sethvoltz/launch_control/media/build-photos/05 - Component detail sketch - USB female socket.jpg

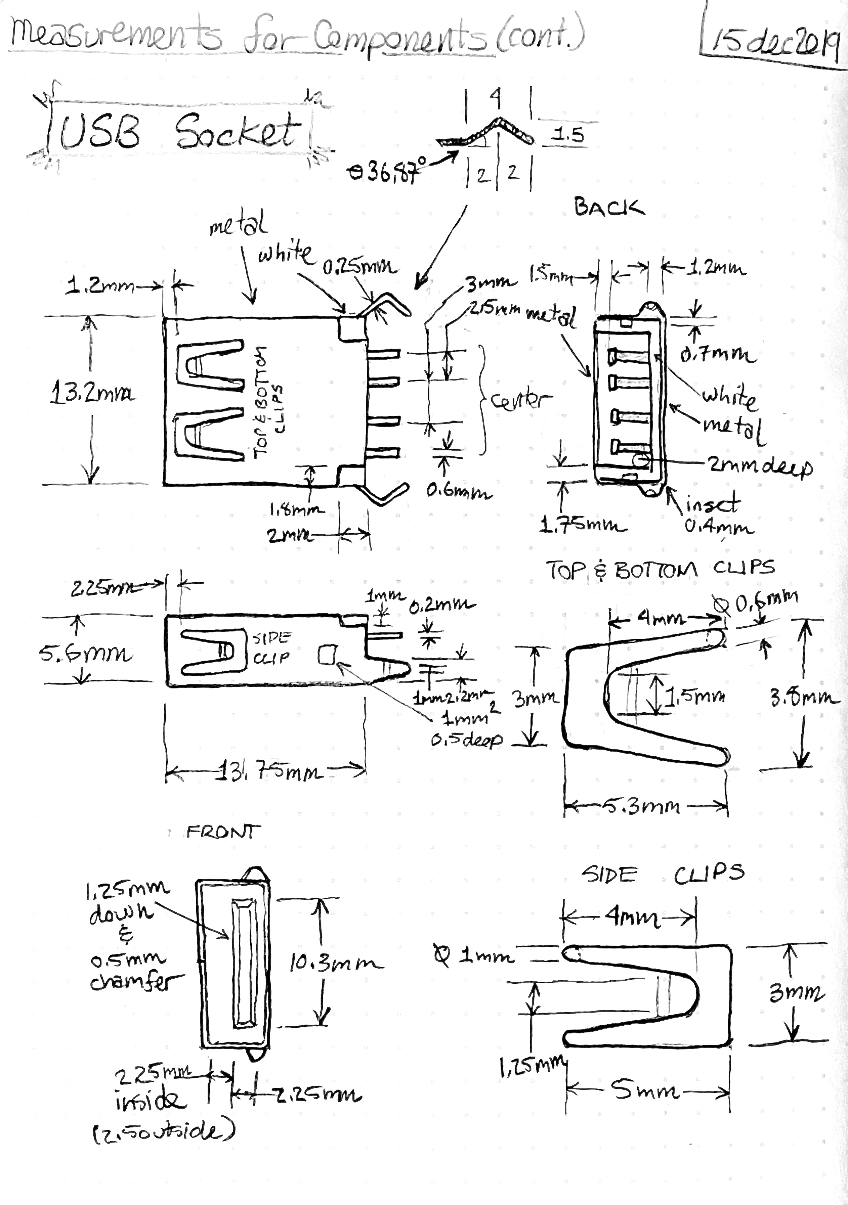
media/build-photos/05 - Component detail sketch - USB female socket.jpg
