sethvoltz/launch_control/media/build-photos/07 - First breadboard prototypes.jpg

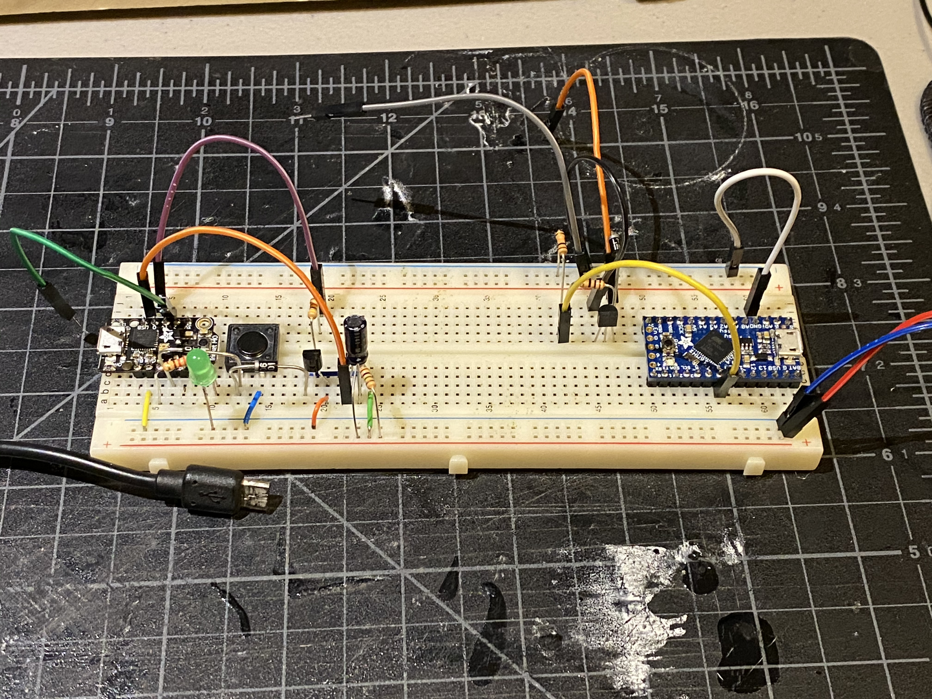
media/build-photos/07 - First breadboard prototypes.jpg
