sethvoltz/launch_control/media/build-photos/09 - Wiring diagram for breakout terminals.jpg

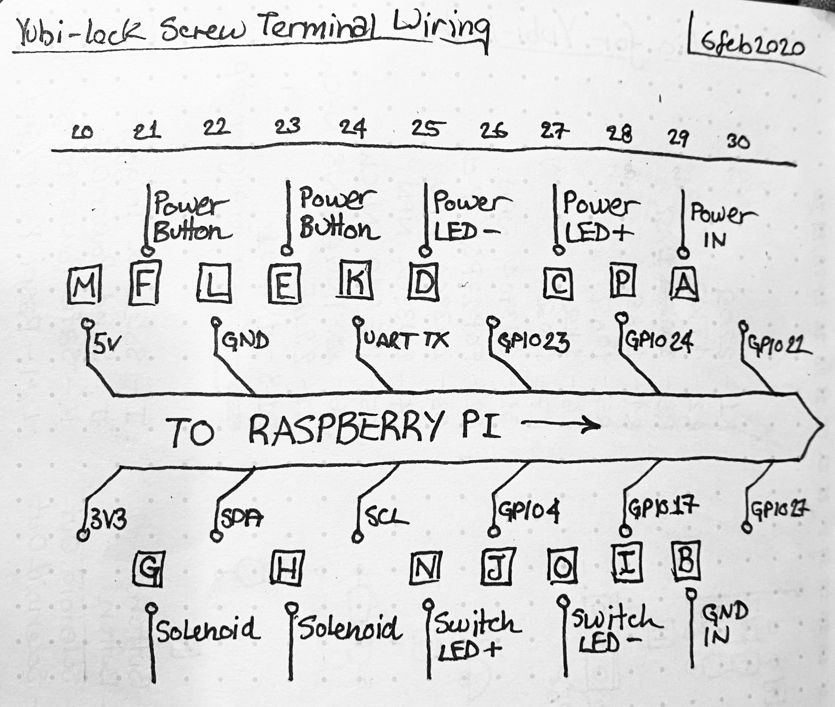
media/build-photos/09 - Wiring diagram for breakout terminals.jpg
