sethvoltz/launch_control/media/build-photos/10 - Board layout for breakout perma-proto board.jpg

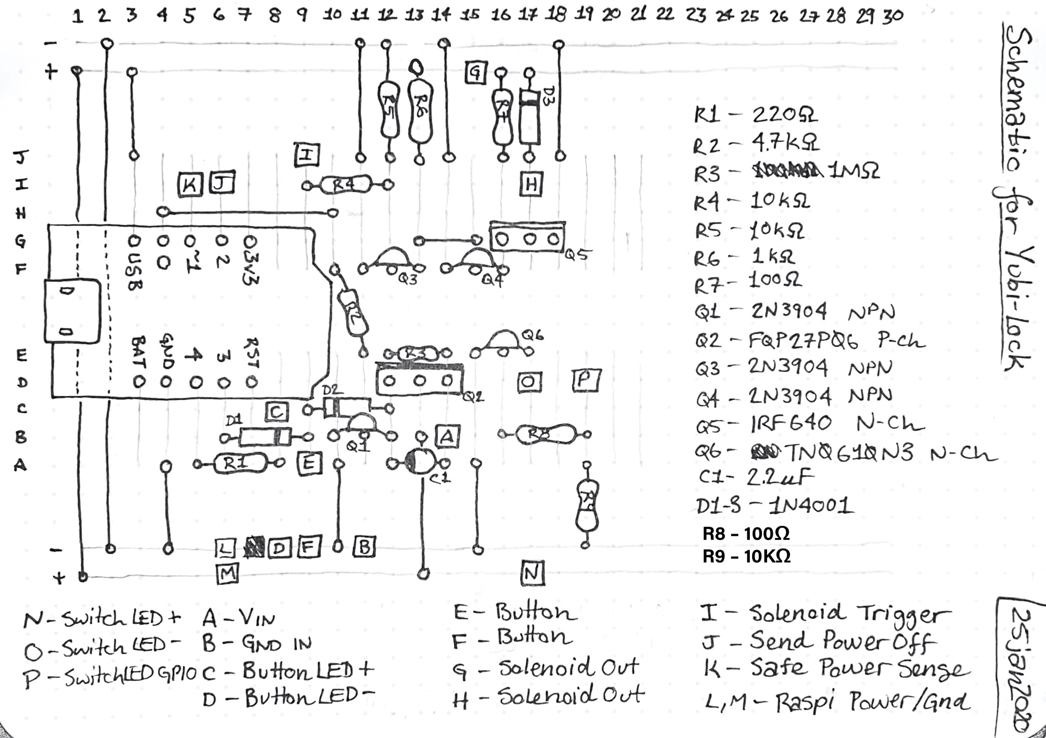
media/build-photos/10 - Board layout for breakout perma-proto board.jpg
