sethvoltz/launch_control/media/build-photos/12 - Breakout connector for I2C, button, toggle, keyswitch.jpg

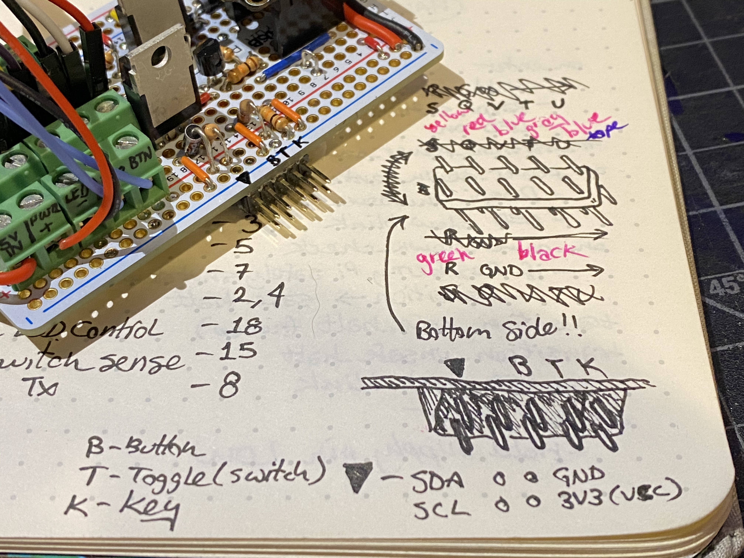
media/build-photos/12 - Breakout connector for I2C, button, toggle, keyswitch.jpg
