sethvoltz/launch_control/media/build-photos/15 - Glamour shot - front.jpg

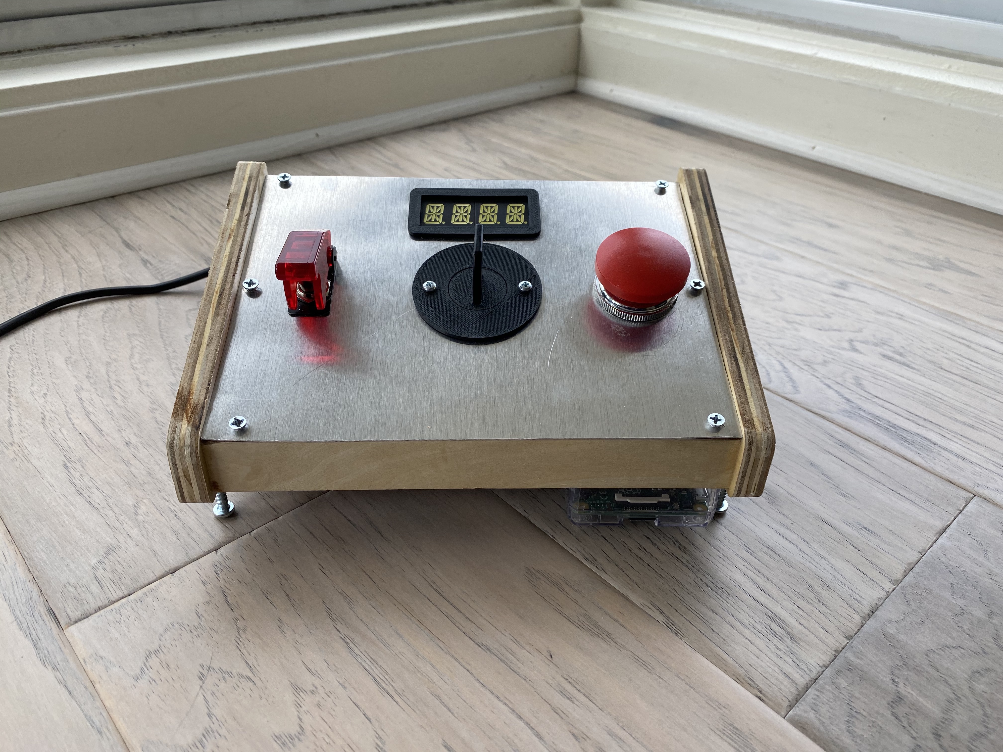
media/build-photos/15 - Glamour shot - front.jpg
