sethvoltz/launch_control/media/build-photos/16 - Glamour shot - left.jpg

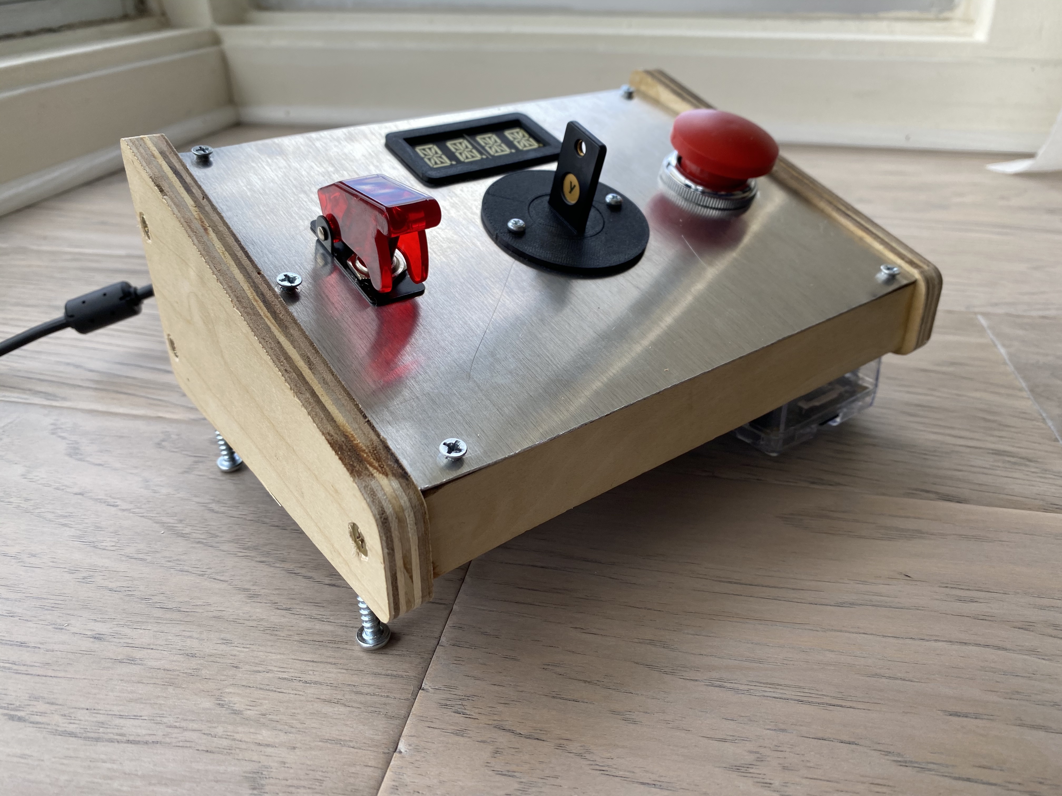
media/build-photos/16 - Glamour shot - left.jpg
