sethvoltz/launch_control/media/build-photos/17 - Glamour shot - back.jpg

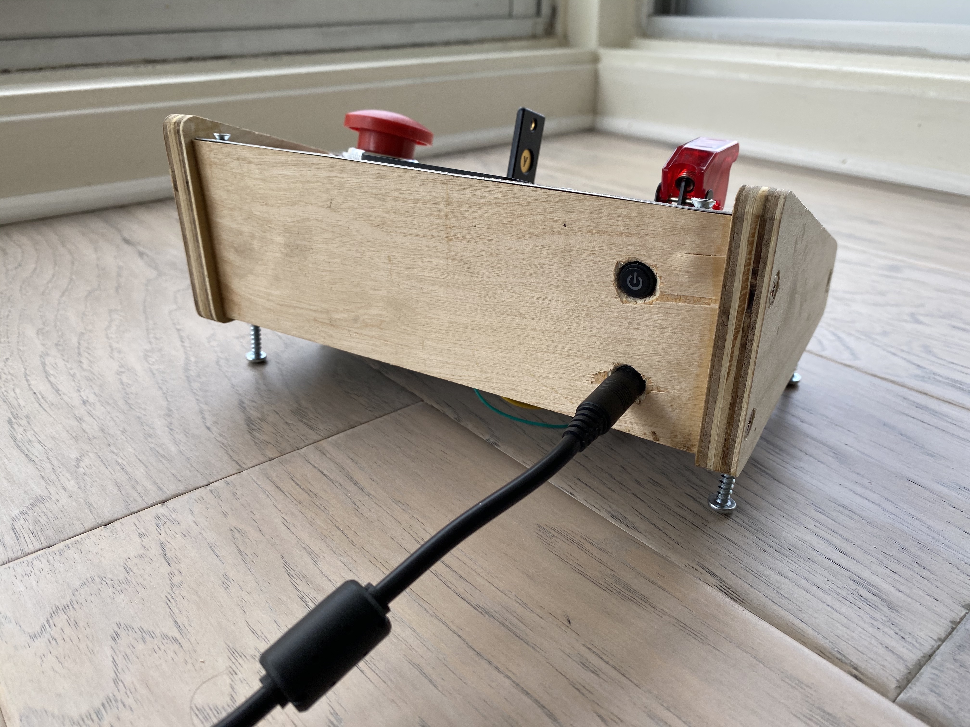
media/build-photos/17 - Glamour shot - back.jpg
