sethvoltz/launch_control/media/build-photos/11 - Perma-proto board rats nest.jpg

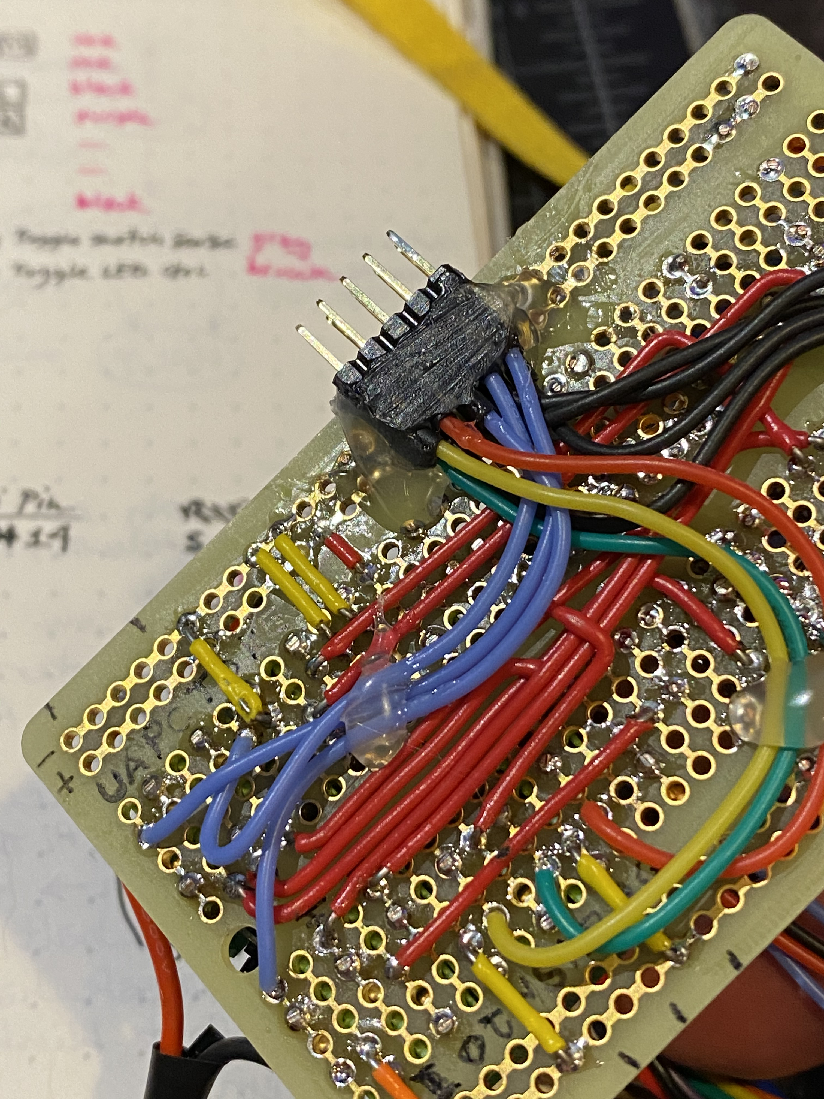
media/build-photos/11 - Perma-proto board rats nest.jpg
