sethvoltz/launch_control/media/build-photos/13 - Assembled Raspberry Pi and breakout board.jpg

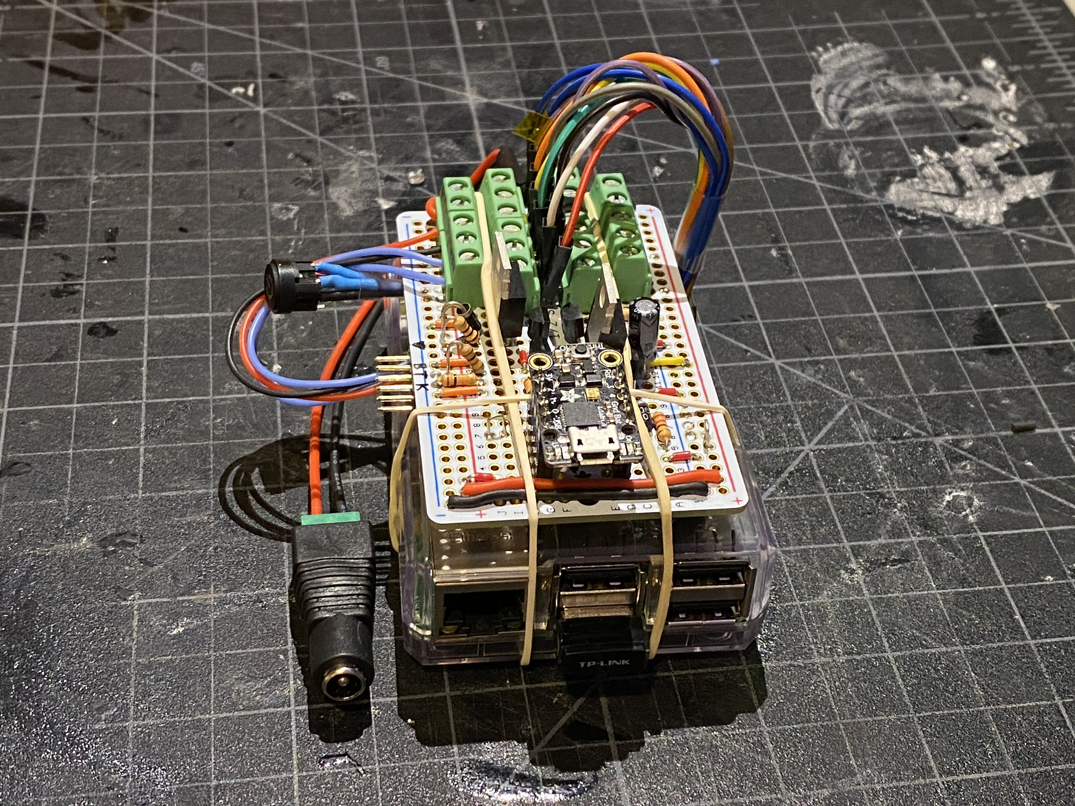
media/build-photos/13 - Assembled Raspberry Pi and breakout board.jpg
