sethvoltz/launch_control/media/build-photos/14 - First boot with everything in the case.jpg

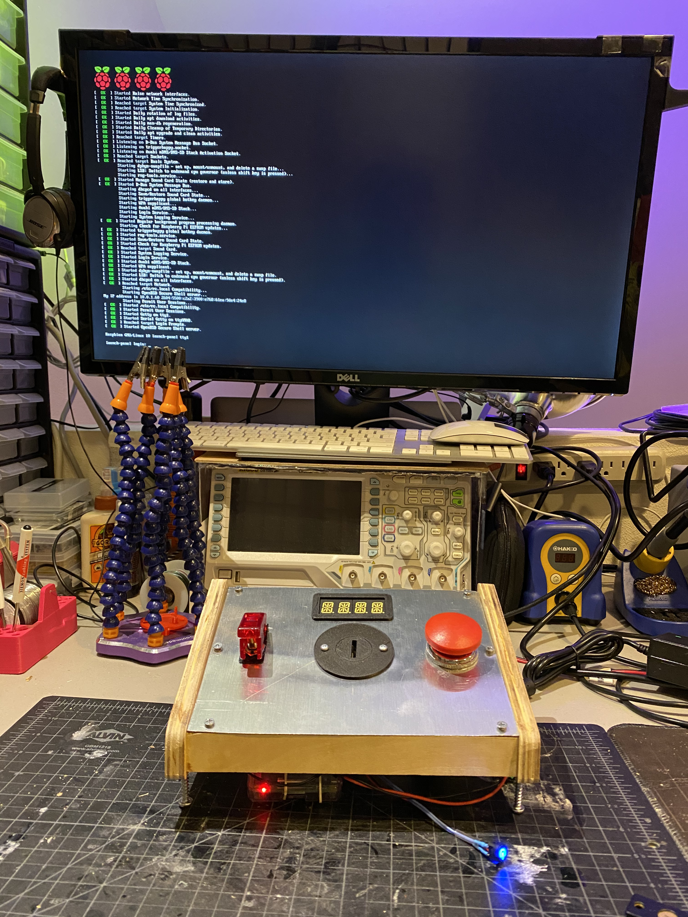
media/build-photos/14 - First boot with everything in the case.jpg
